jorgeedribeiro2001/data_logger/Tests and Results/Vibration Validation Test/Setup Images/foto_vibracao.jpg

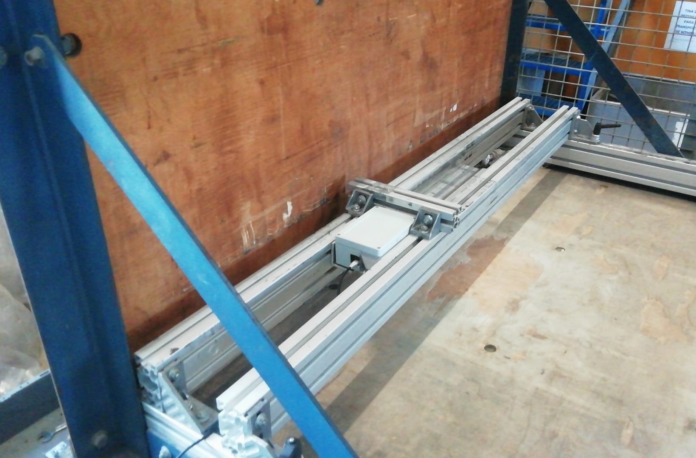
Tests and Results/Vibration Validation Test/Setup Images/foto_vibracao.jpg
