jorgeedribeiro2001/data_logger/Tests and Results/Vibration Validation Test/Setup Images/IMG-20240514-WA0013.jpg

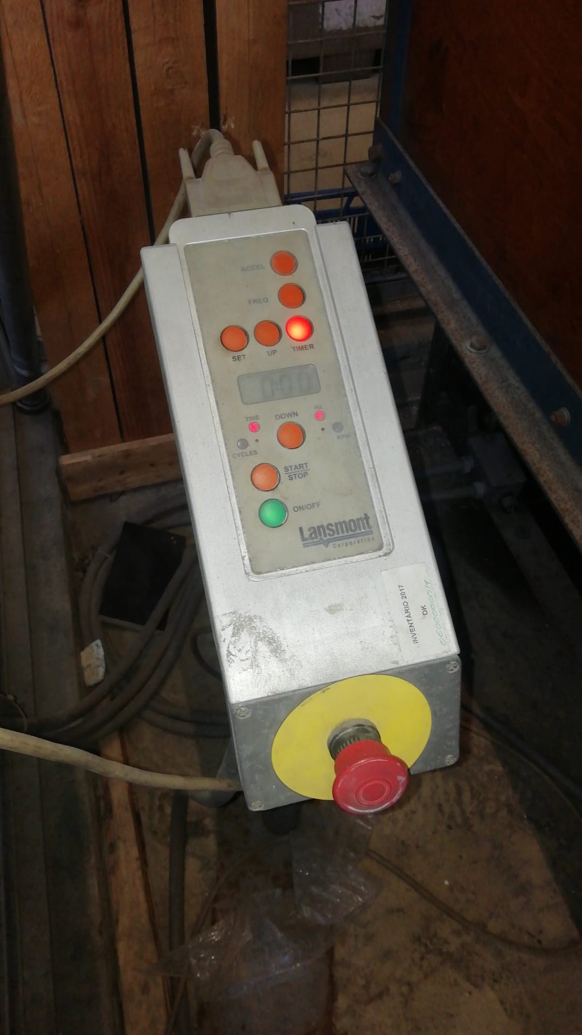
Tests and Results/Vibration Validation Test/Setup Images/IMG-20240514-WA0013.jpg
