jorgeedribeiro2001/data_logger/Tests and Results/Robustness Tests/RE04_Electronics Storage Robustness Test/humidity.jpeg

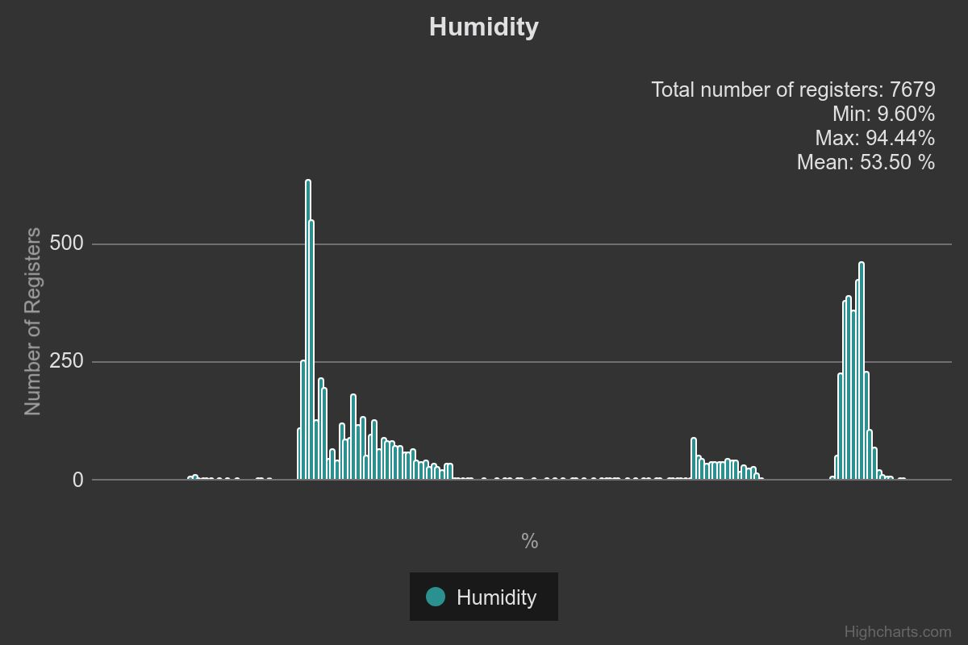
Tests and Results/Robustness Tests/RE04_Electronics Storage Robustness Test/humidity.jpeg
