jorgeedribeiro2001/data_logger/Tests and Results/Temperature Validation Test/Fotos/fig1_temp_test.jpg

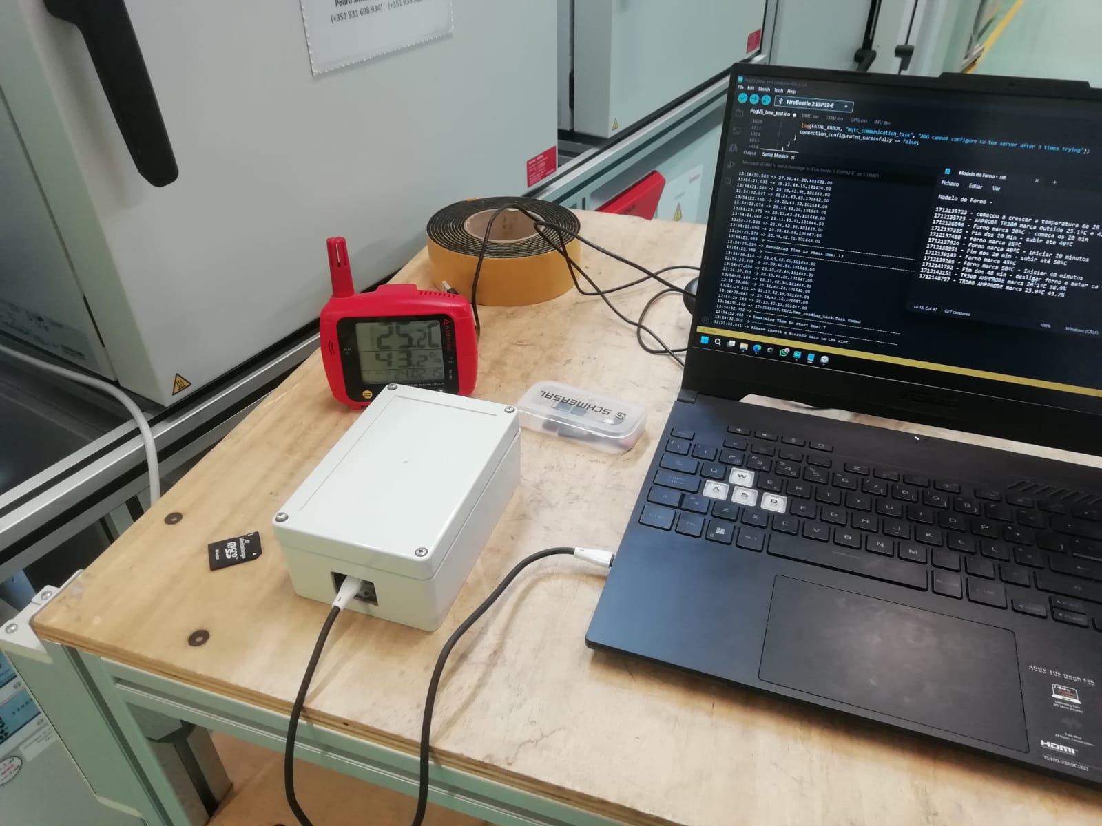
Tests and Results/Temperature Validation Test/Fotos/fig1_temp_test.jpg
