jorgeedribeiro2001/data_logger/Tests and Results/Temperature Validation Test/Fotos/fig2_temp_test - Cópia.jpg

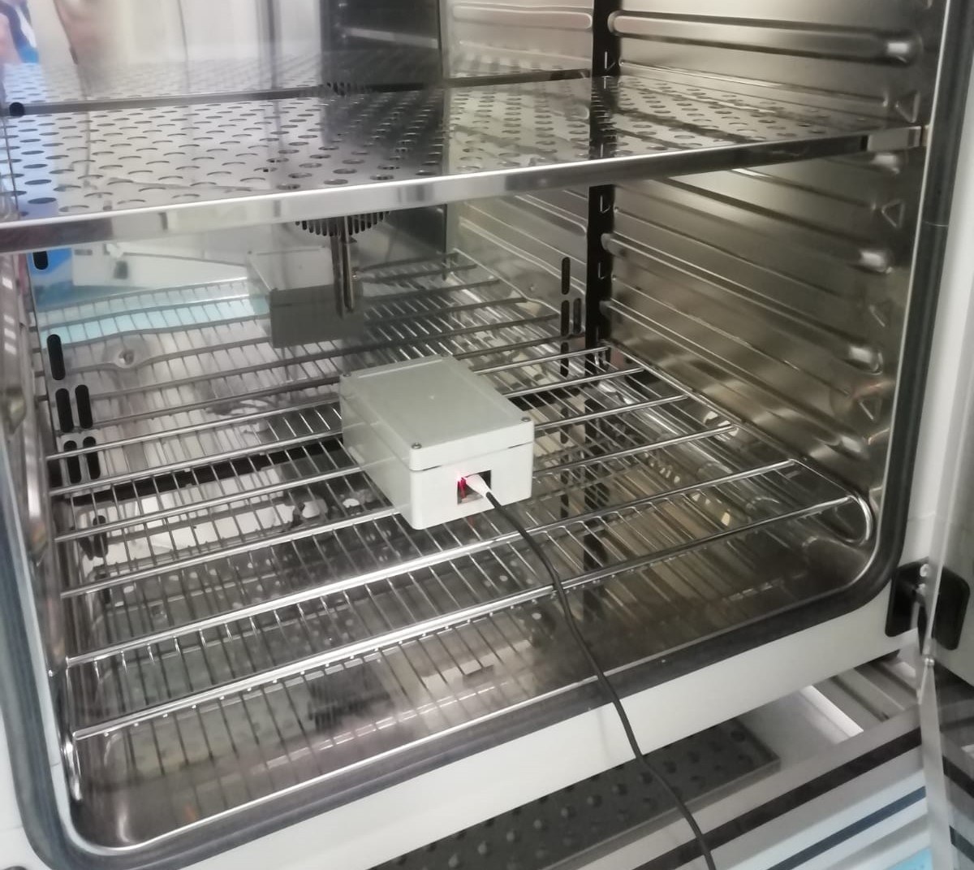
Tests and Results/Temperature Validation Test/Fotos/fig2_temp_test - Cópia.jpg
