jorgeedribeiro2001/data_logger/Tests and Results/Temperature Validation Test/Fotos/fig2_temp_test.jpg

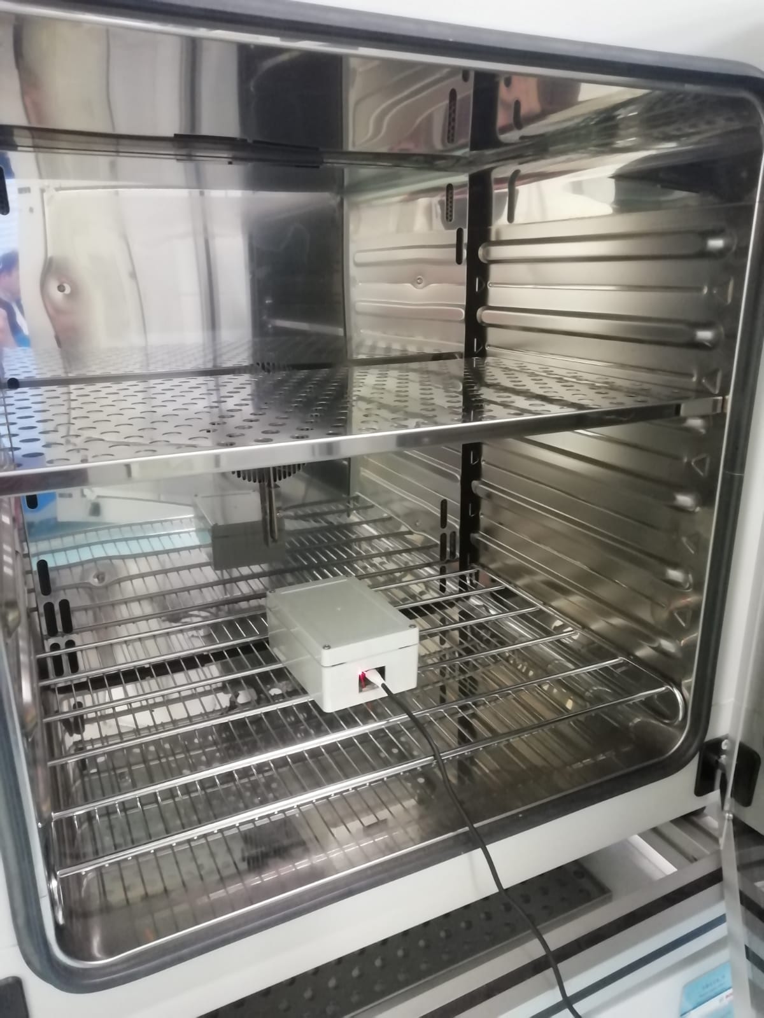
Tests and Results/Temperature Validation Test/Fotos/fig2_temp_test.jpg
