jorgeedribeiro2001/data_logger/Tests and Results/Temperature Validation Test/Fotos/IMG-20240403-WA0004.jpg

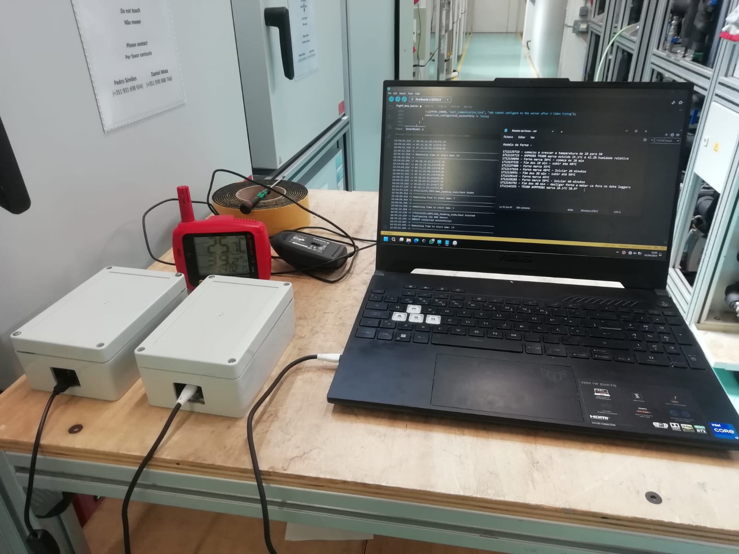
Tests and Results/Temperature Validation Test/Fotos/IMG-20240403-WA0004.jpg
