jorgeedribeiro2001/data_logger/Tests and Results/Temperature Validation Test/graph_temp_test.png

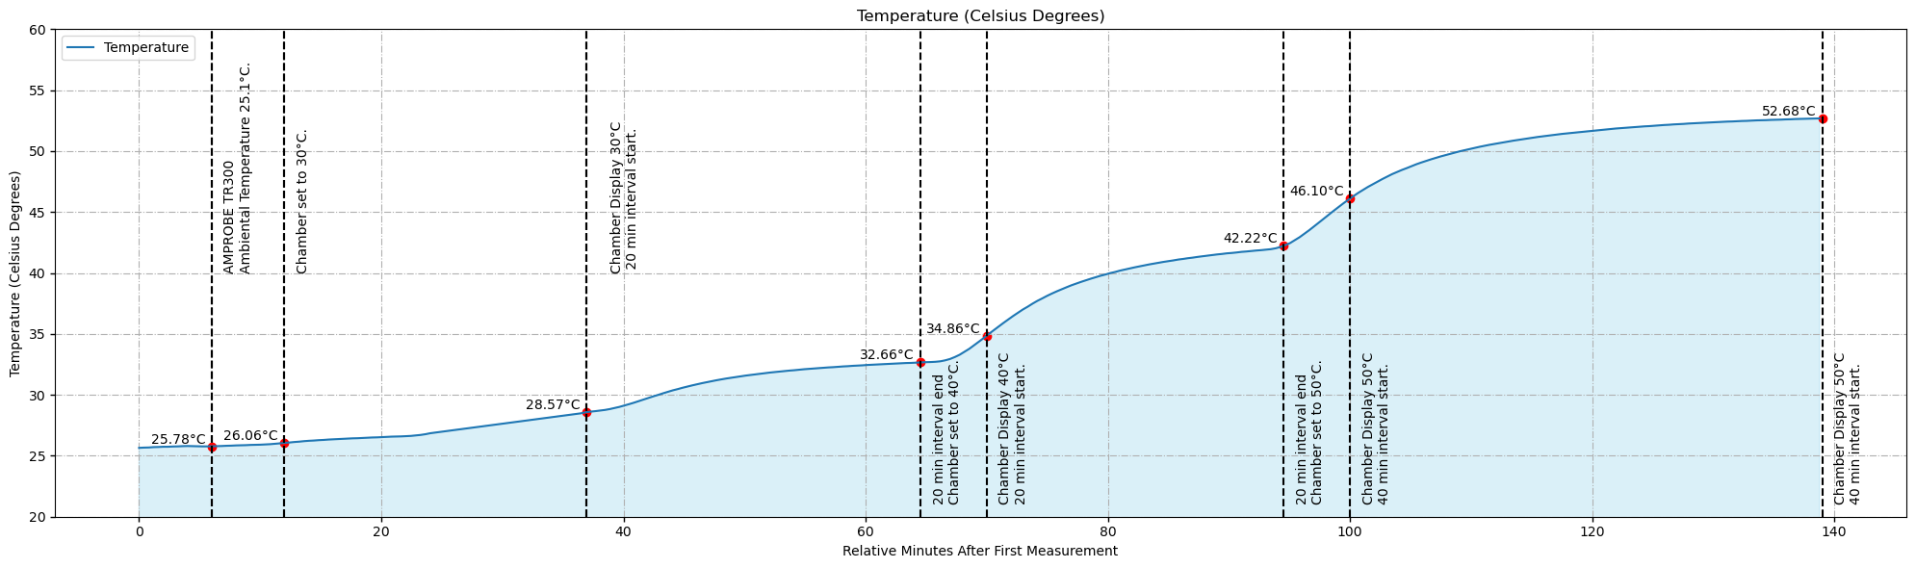
Tests and Results/Temperature Validation Test/graph_temp_test.png
