jorgeedribeiro2001/data_logger/Tests and Results/Temperature Validation Test/graph_temp_test_for_report.png

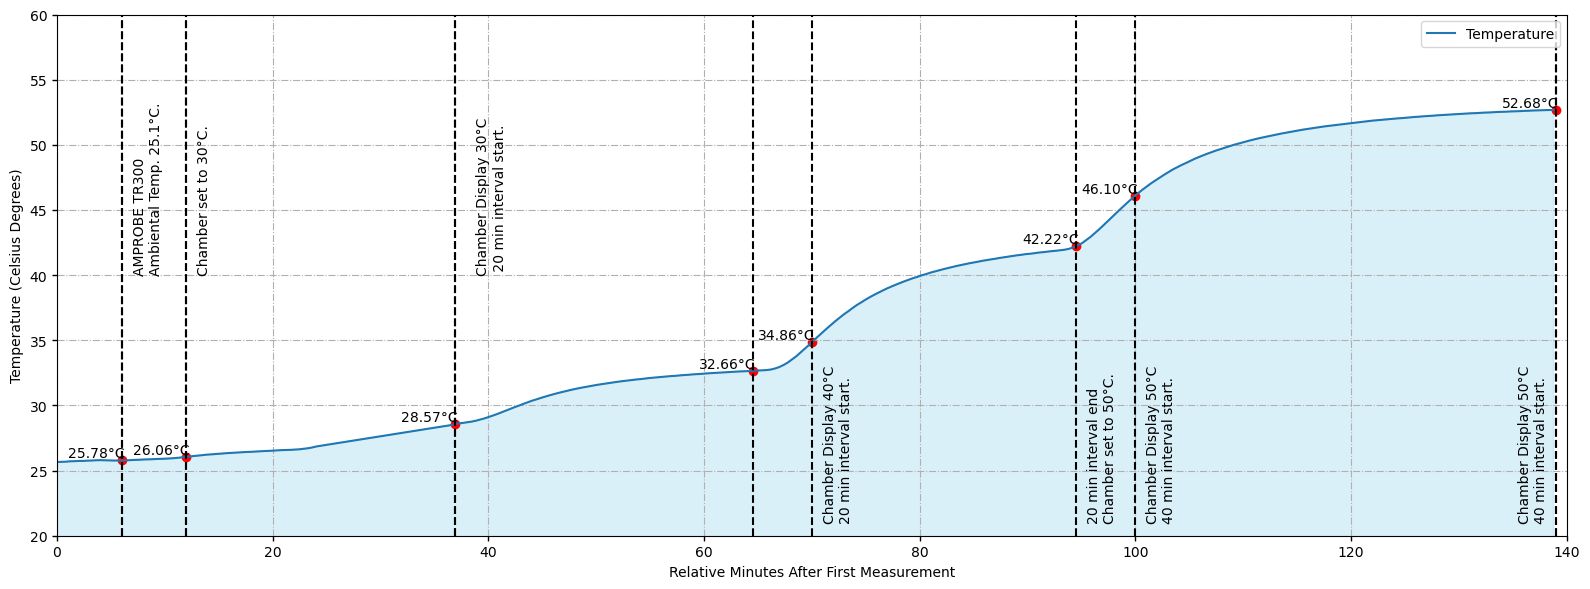
Tests and Results/Temperature Validation Test/graph_temp_test_for_report.png
