jorgeedribeiro2001/data_logger/Tests and Results/Vibration Validation Test/Results/test1_vibration_psd.png

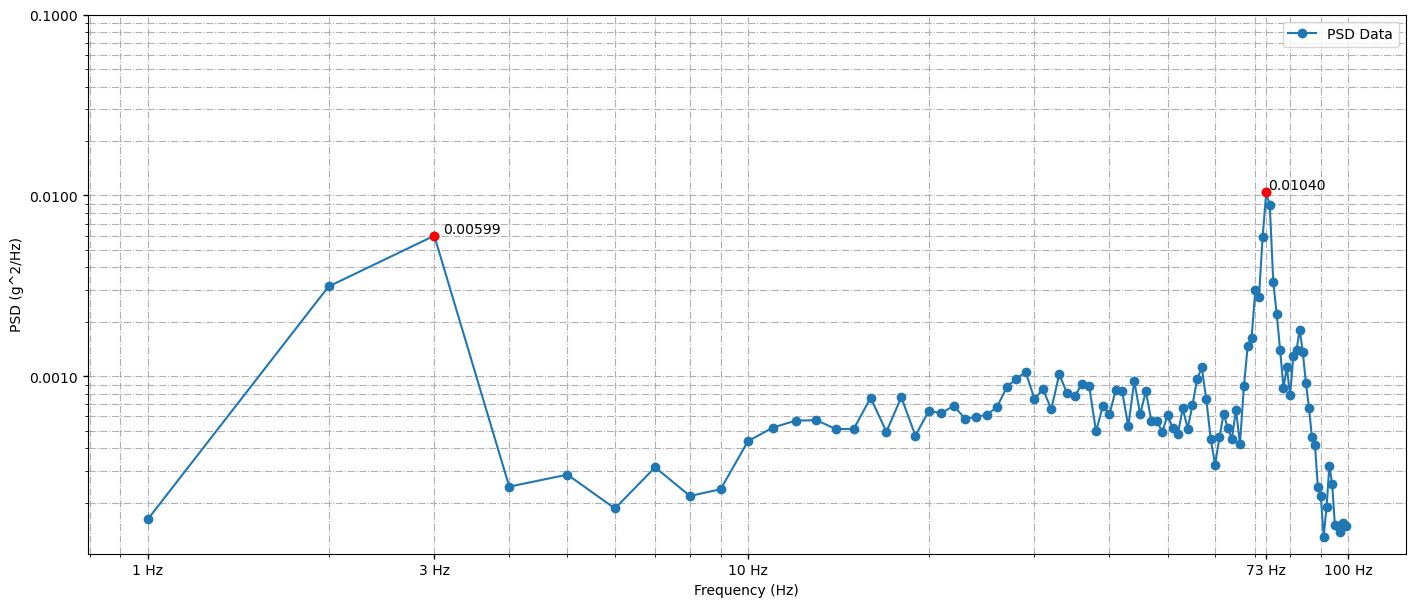
Tests and Results/Vibration Validation Test/Results/test1_vibration_psd.png
